kushurox/fiddlesticks_pcb/fiddlesticks.pdf

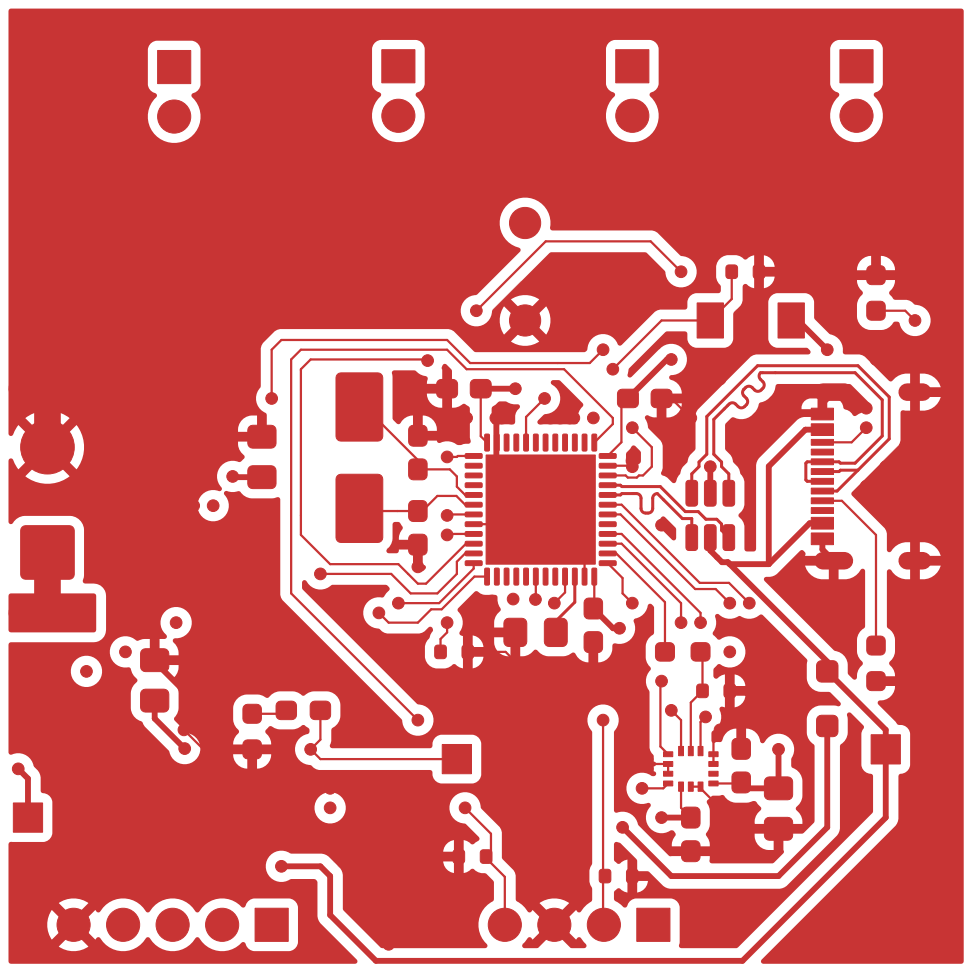
[picture p3: page 1]

Id: 1/11 Title: File: fiddlesticks.kicad_pcb Sheet:

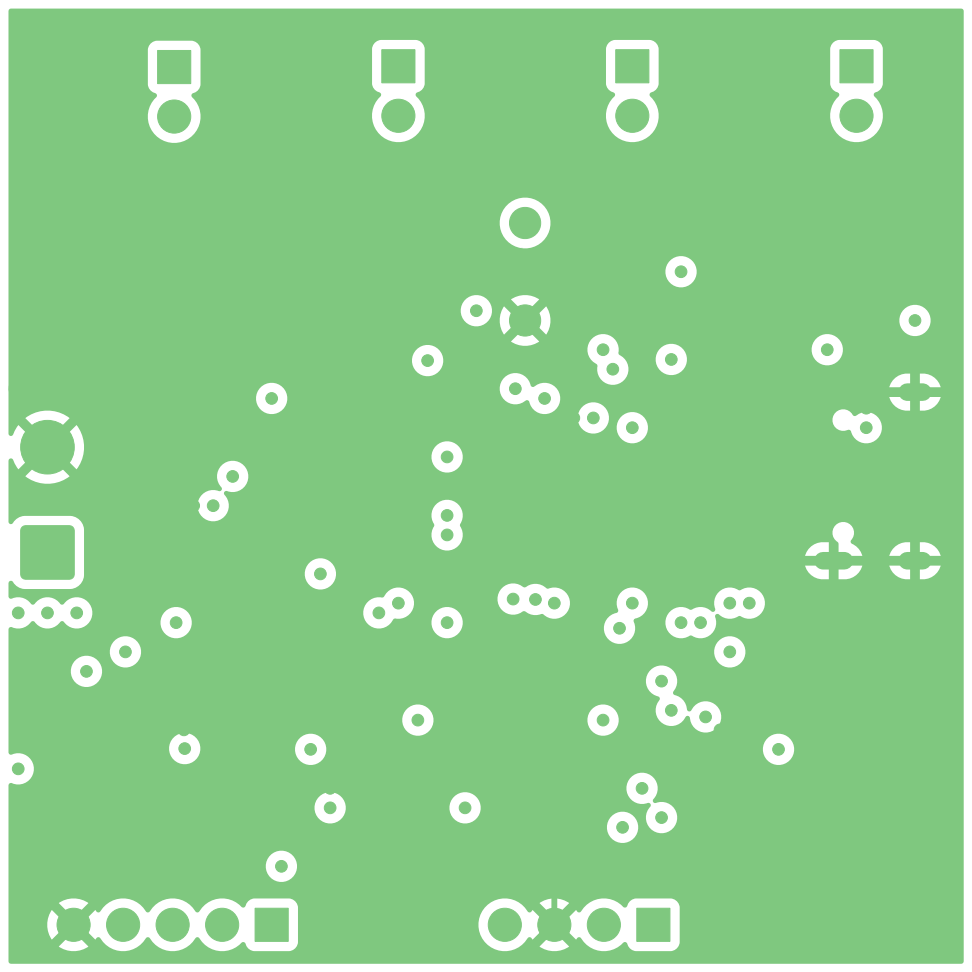
[picture p4: page 2]

Id: 2/11 Title: File: fiddlesticks.kicad_pcb Sheet:

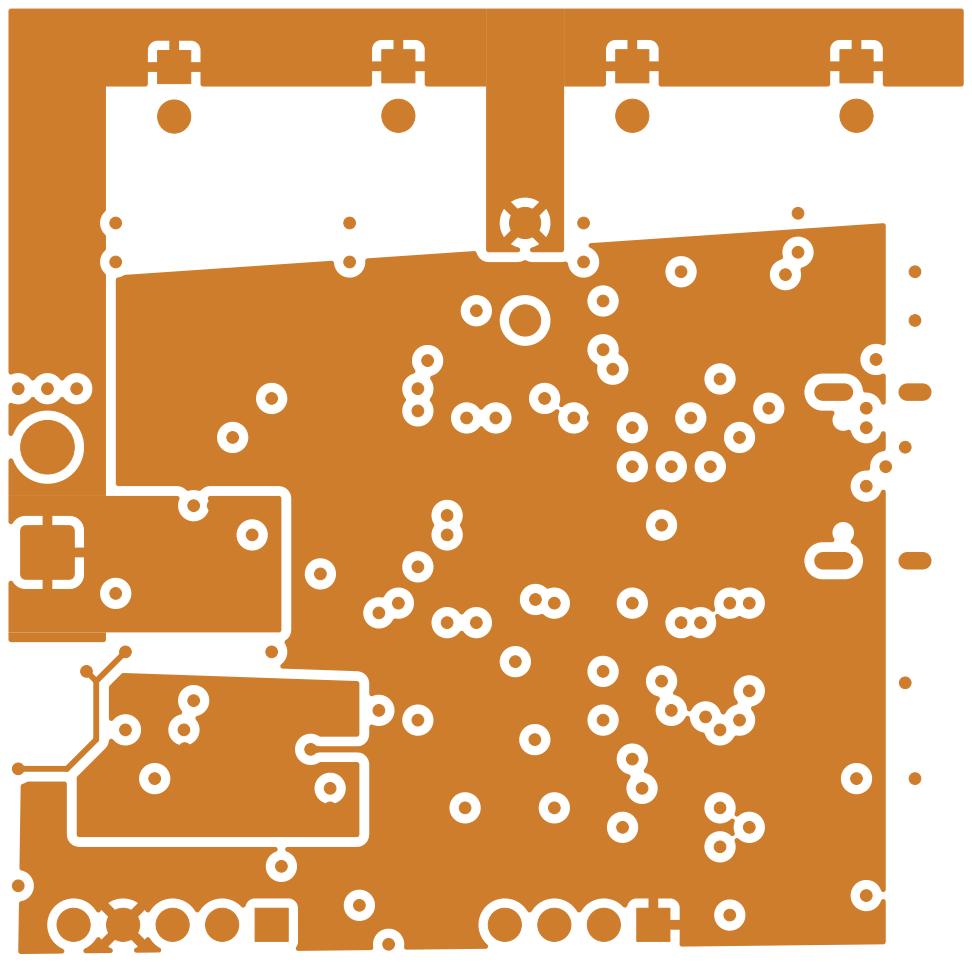
[picture p5: page 3]

Id: 3/11 Title: File: fiddlesticks.kicad_pcb Sheet:

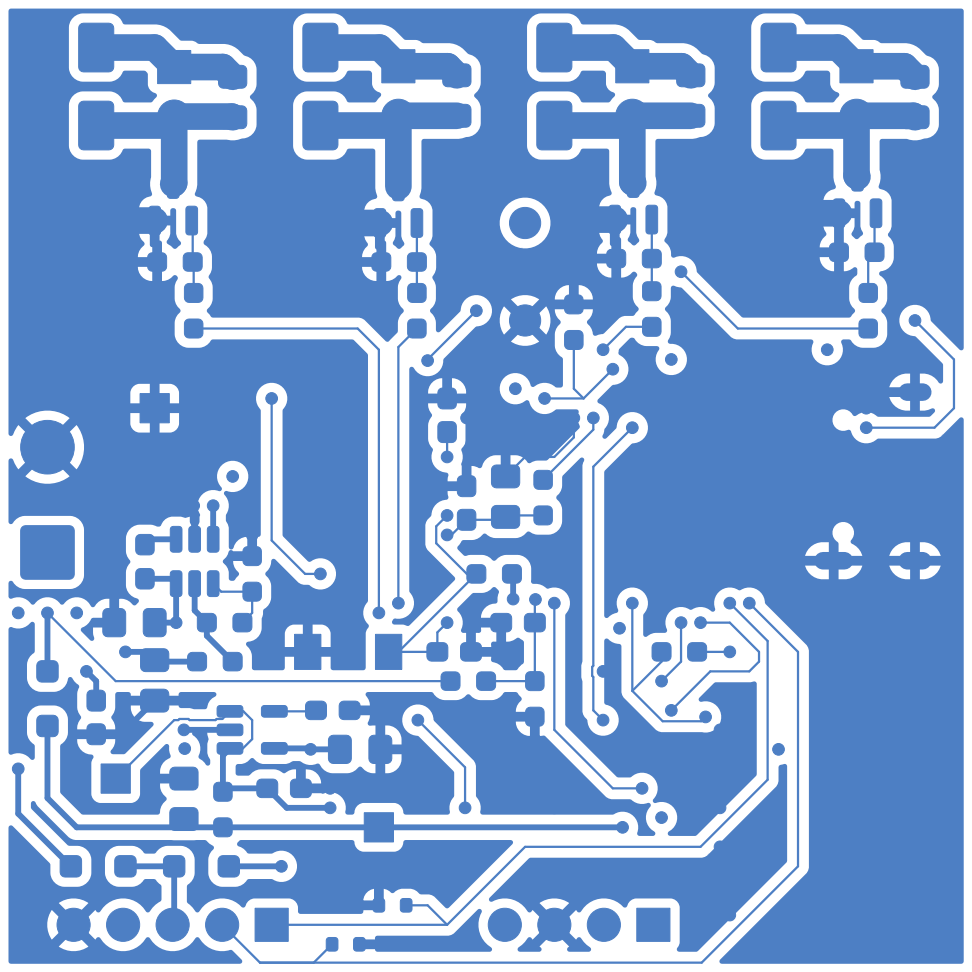
[picture p6: page 4]

Id: 4/11 Title: File: fiddlesticks.kicad_pcb Sheet:

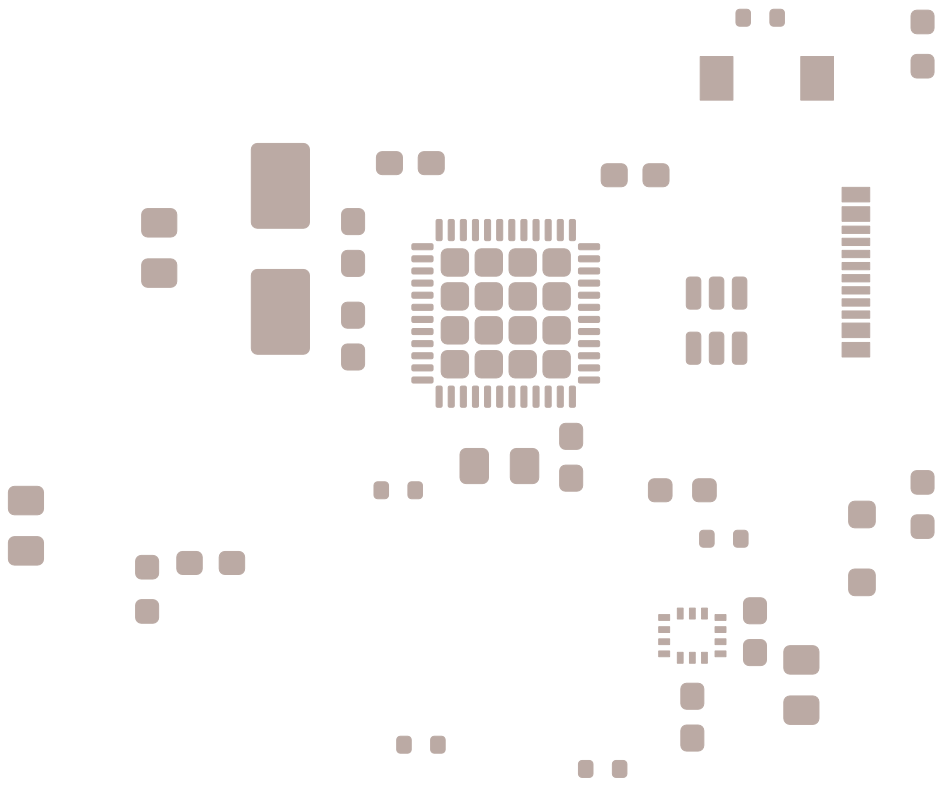
[picture p7: page 5]

Id: 5/11 Title: File: fiddlesticks.kicad_pcb Sheet:

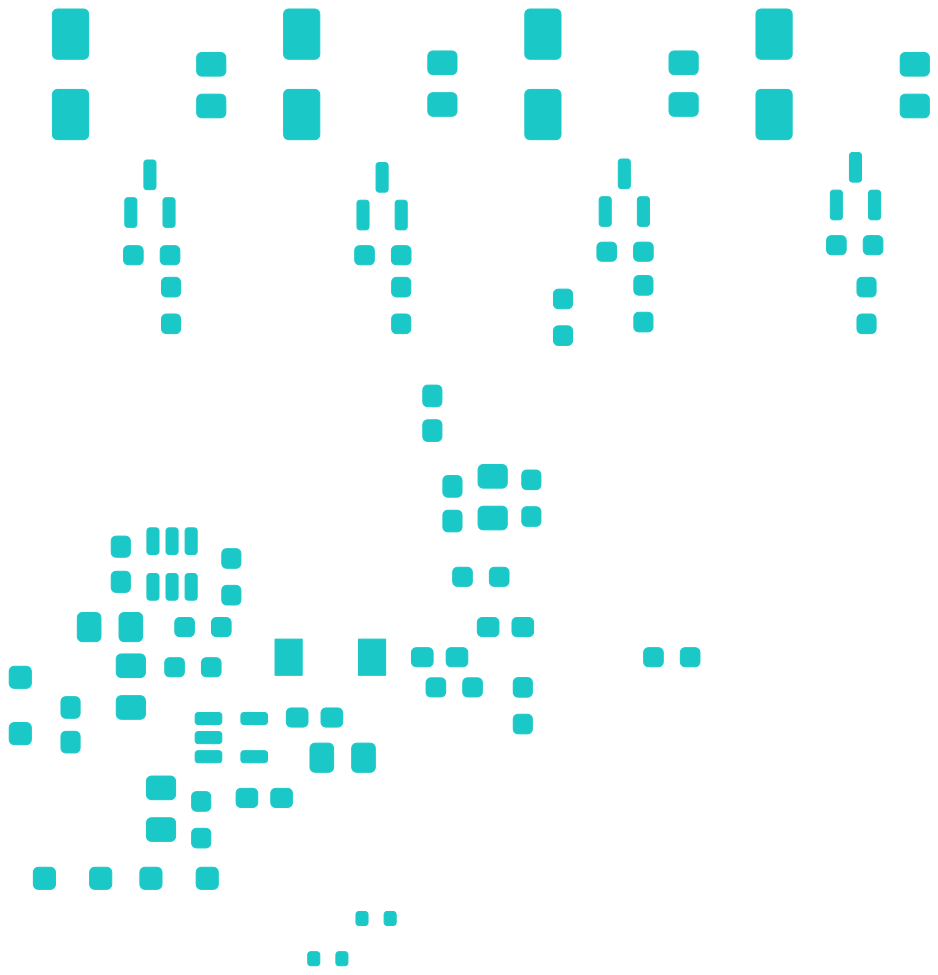
[picture p8: page 6]

Id: 6/11 Title: File: fiddlesticks.kicad_pcb Sheet:

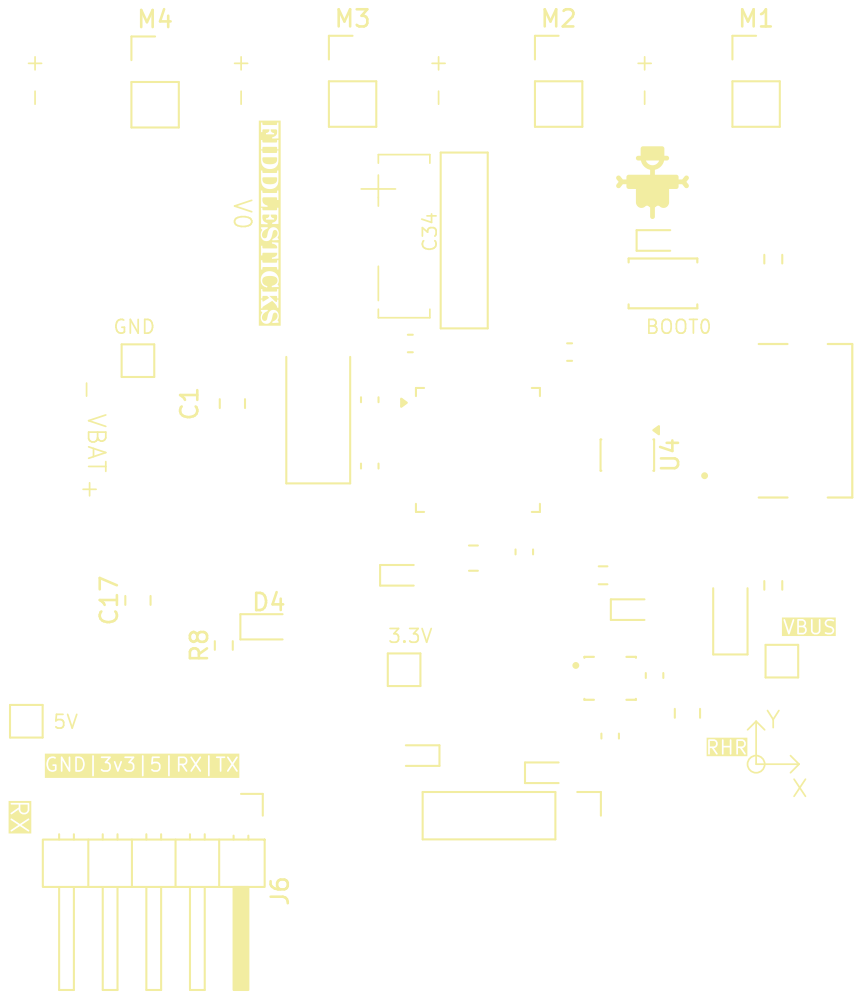
[picture p9: page 7]

Id: 7/11 Title: File: fiddlesticks.kicad_pcb Sheet:

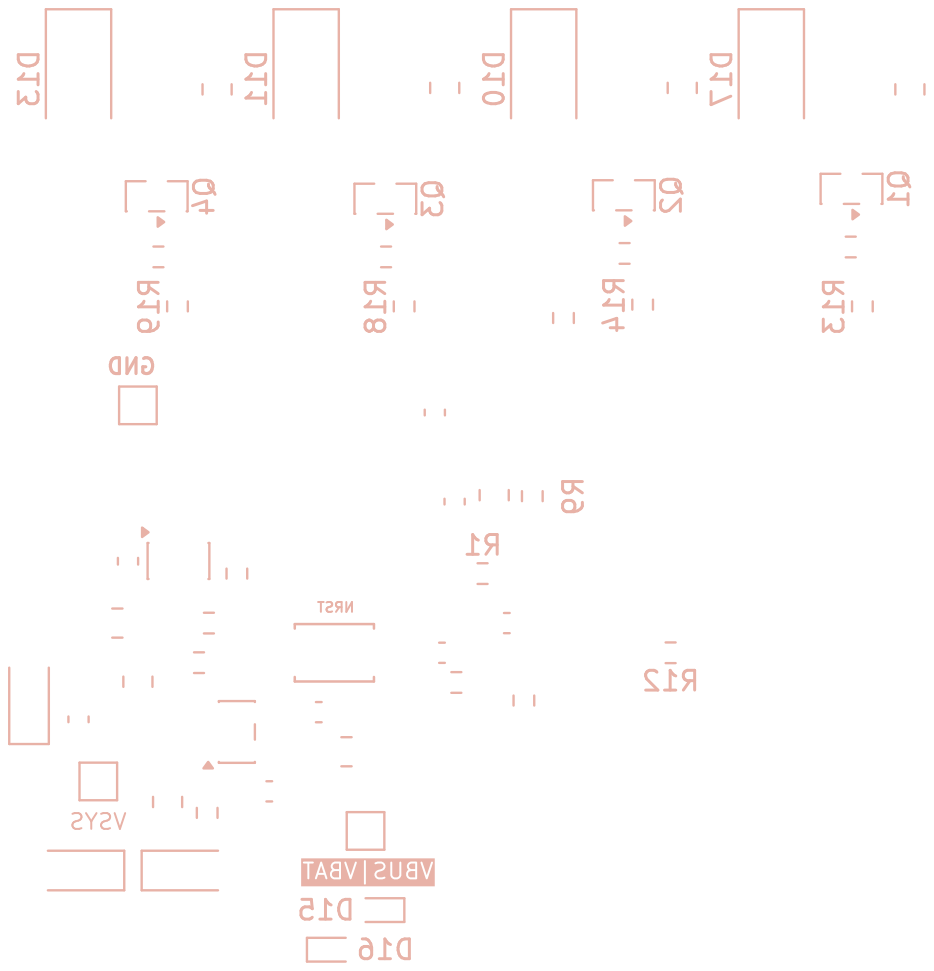
[picture p10: page 8]

Id: 8/11 Title: File: fiddlesticks.kicad_pcb Sheet:

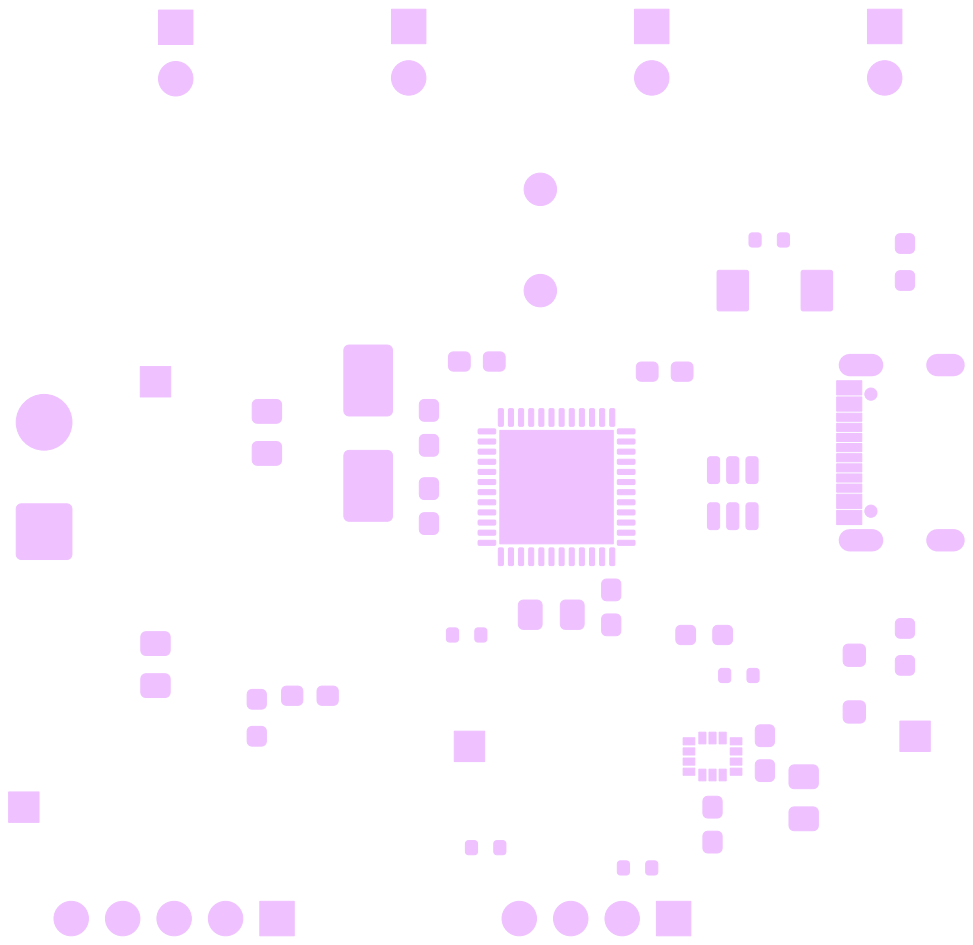
[picture p11: page 9]

Id: 9/11 Title: File: fiddlesticks.kicad_pcb Sheet:

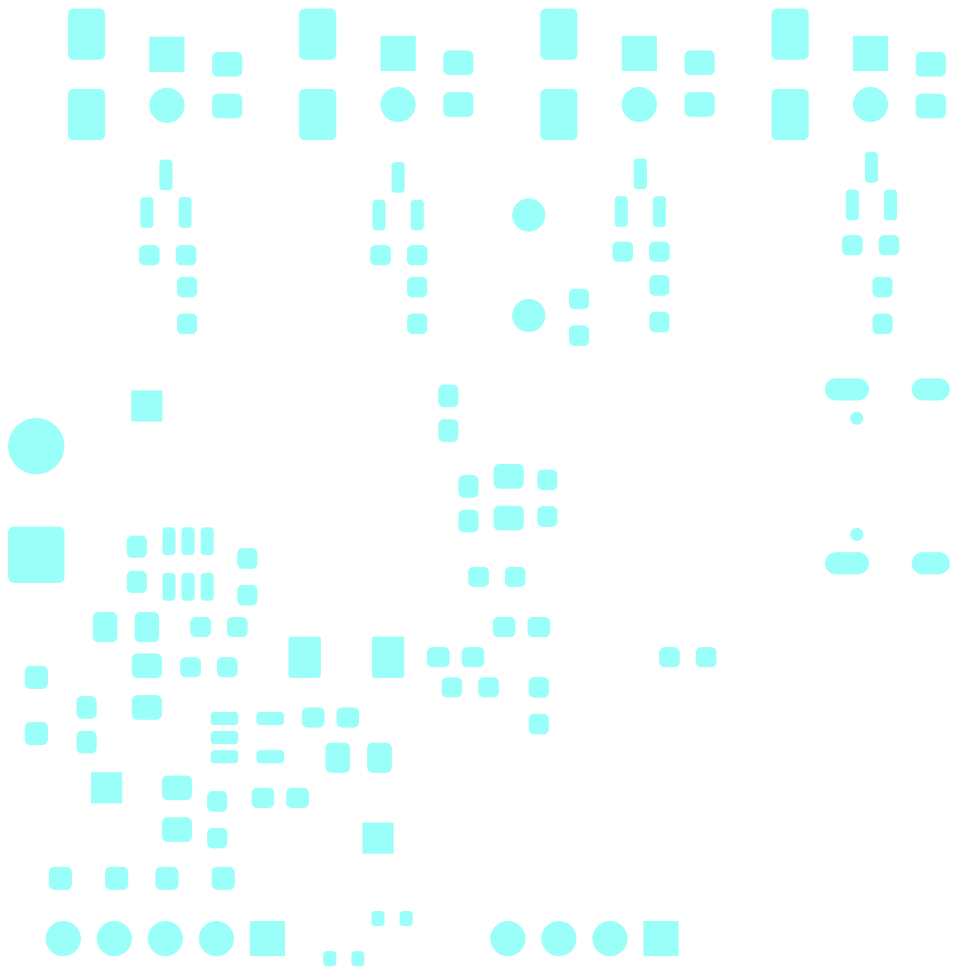
[picture p12: page 10]

Id: 10/11 Title: File: fiddlesticks.kicad_pcb Sheet:

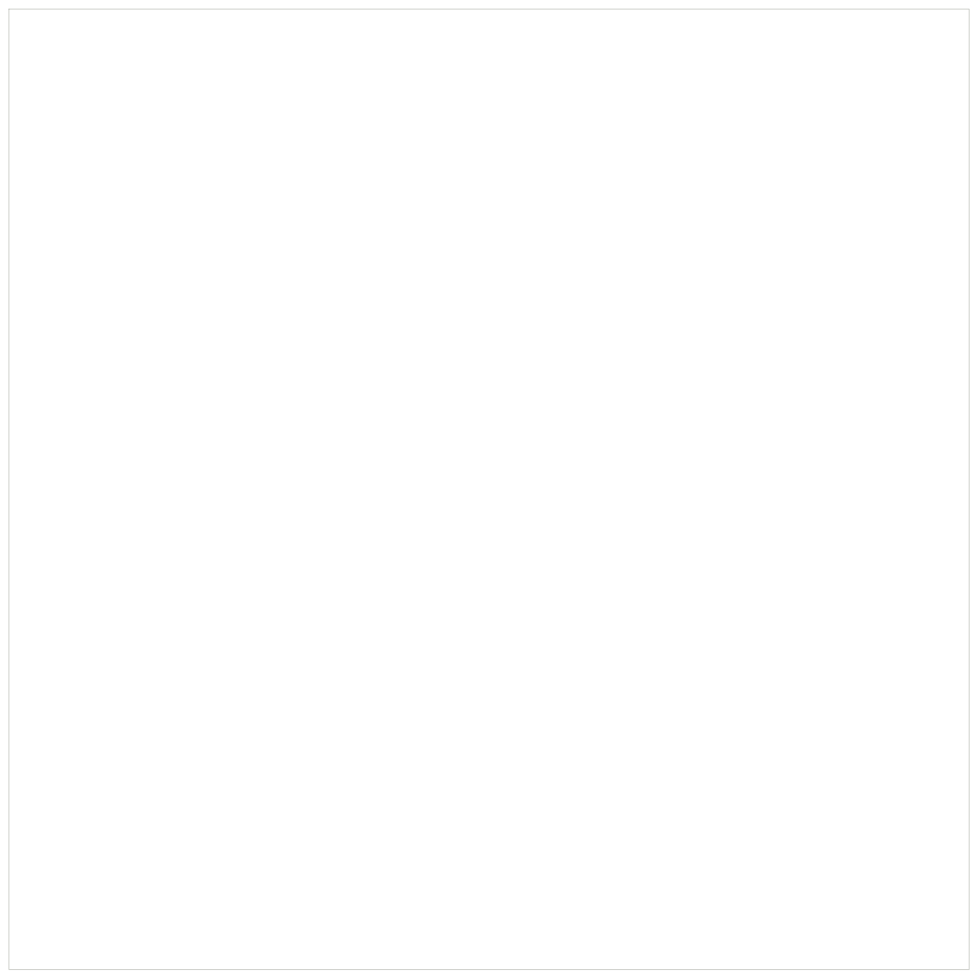
[picture p13: page 11]

Id: 11/11 Title: File: fiddlesticks.kicad_pcb Sheet:
